pila81/Trident_Mods/Z_Carriages_FLEX/STL/z_carriage_rear_spacer_FLEX.stl

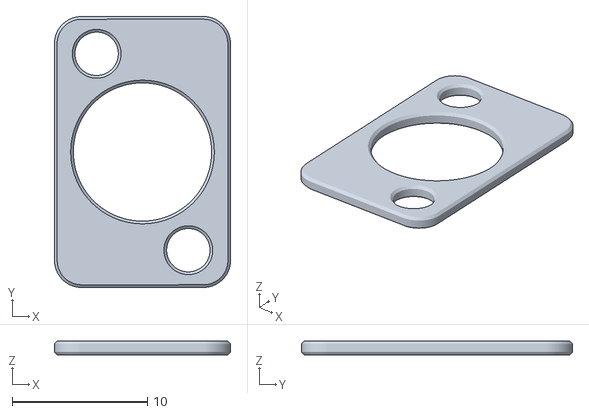
[picture p46: CAD file, 2023-04-26]
Z_Carriages_FLEX/STL/z_carriage_rear_spacer_FLEX.stl
13.0 x 20.0 x 1.00
