pila81/Trident_Mods/AB_Stepper_Mounts_Pin_Bearing/STL/a_drive_frame_upper_pin_bear.stl

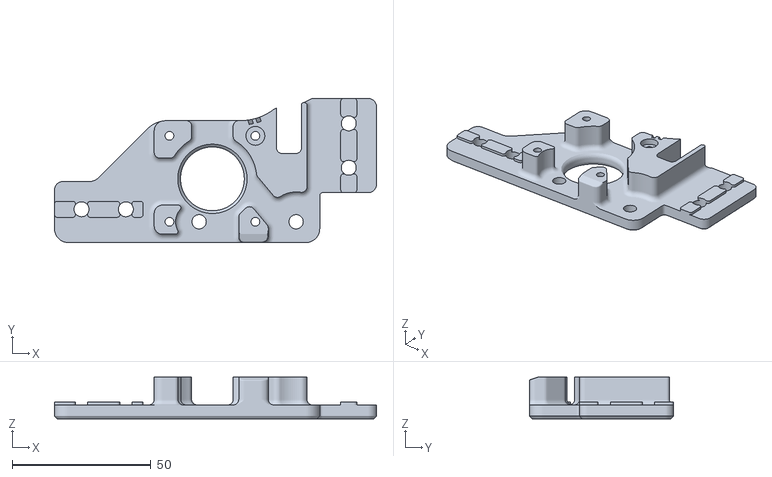
[picture p47: CAD file, 2023-05-03]
AB_Stepper_Mounts_Pin_Bearing/STL/a_drive_frame_upper_pin_bear.stl
116.2 x 52.0 x 15.0
