pila81/Trident_Mods/Idlers_Tensioners_Aligned/STL/[a]_tensioner_left.stl

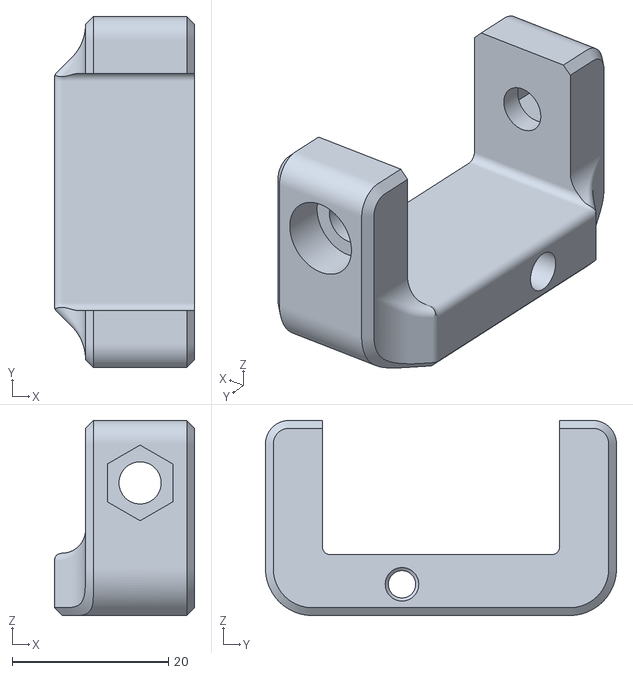
[picture p48: CAD file, 2022-02-14]
Idlers_Tensioners_Aligned/STL/[a]_tensioner_left.stl
18.0 x 45.0 x 25.0
