pila81/Trident_Mods/Z_Carriages_FLEX/STL/[a]z_carriage_rear_3hole_FLEX.stl

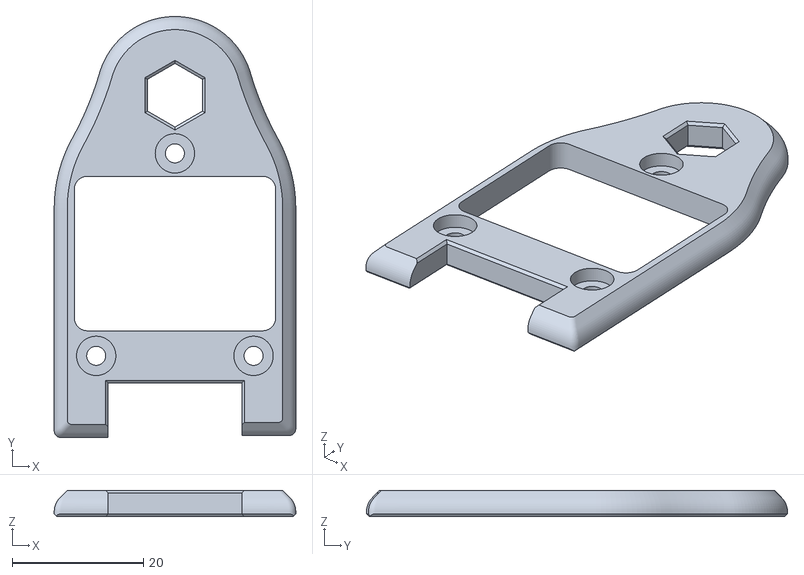
[picture p49: CAD file, 2023-04-26]
Z_Carriages_FLEX/STL/[a]z_carriage_rear_3hole_FLEX.stl
36.8 x 64.2 x 4.00
