pila81/Trident_Mods/AB_Stepper_Mounts_Pin_Bearing/STL/b_drive_frame_lower_pin_bear.stl

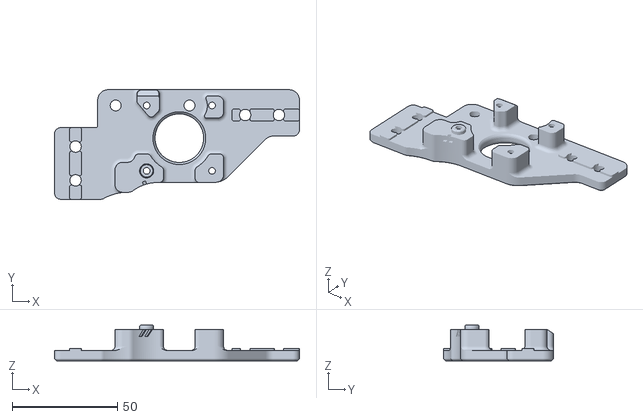
[picture p50: CAD file, 2023-05-03]
AB_Stepper_Mounts_Pin_Bearing/STL/b_drive_frame_lower_pin_bear.stl
116.2 x 52.0 x 17.0
