pila81/Trident_Mods/Exhaust_HEPA_Filter_Small/STL/Fan_Mount.stl

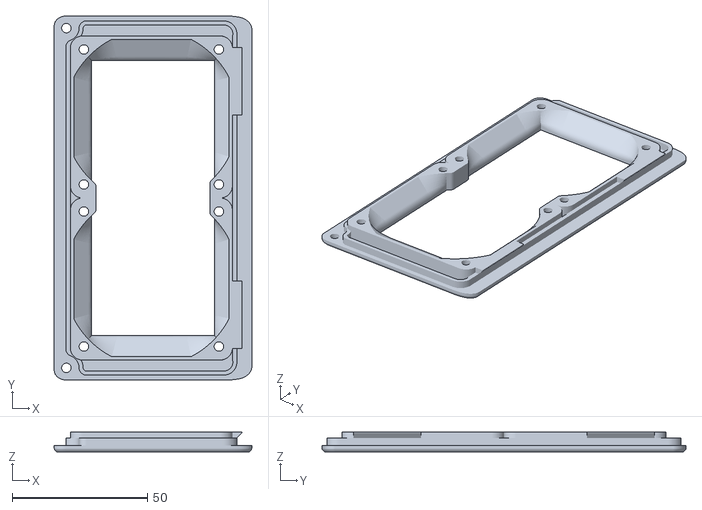
[picture p51: CAD file, 2022-02-18]
Exhaust_HEPA_Filter_Small/STL/Fan_Mount.stl
73.2 x 134.8 x 7.40
