pila81/Trident_Mods/Z_Carriages_FLEX/STL/z_carriage_right_FLEX.stl

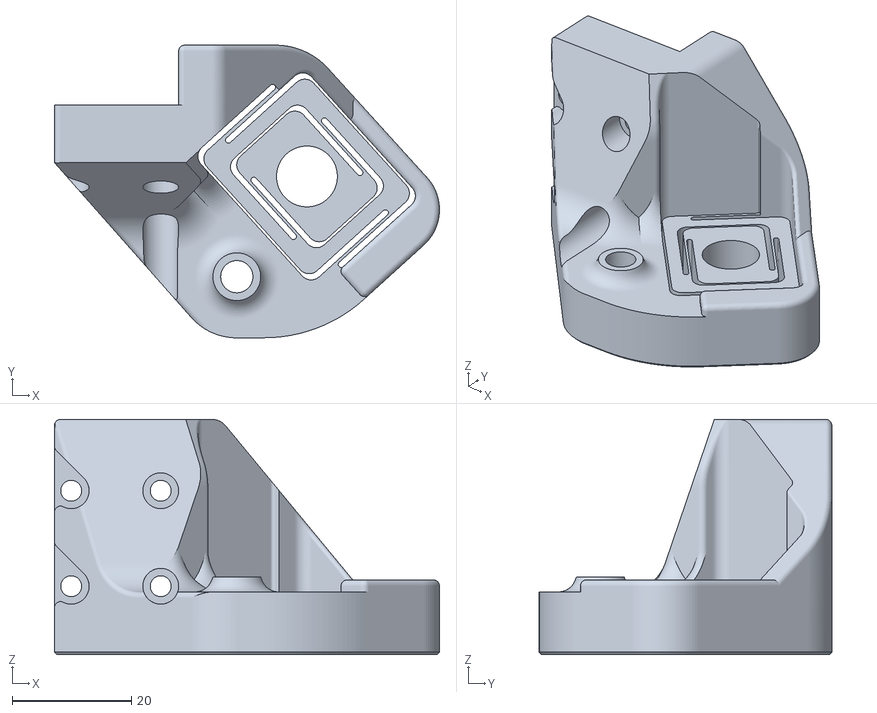
[picture p52: CAD file, 2023-04-26]
Z_Carriages_FLEX/STL/z_carriage_right_FLEX.stl
64.5 x 49.1 x 39.4
