pila81/Trident_Mods/Z_Carriages_FLEX/STL/[a]z_carriage_right_FLEX.stl

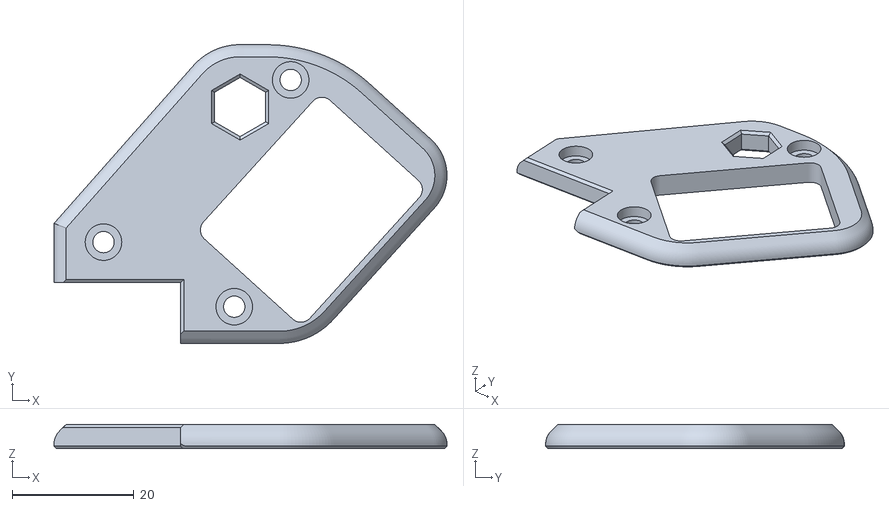
[picture p53: CAD file, 2023-04-26]
Z_Carriages_FLEX/STL/[a]z_carriage_right_FLEX.stl
64.5 x 49.0 x 4.00
